lucabotez/OpenBook/Images/3D PCB.JPG

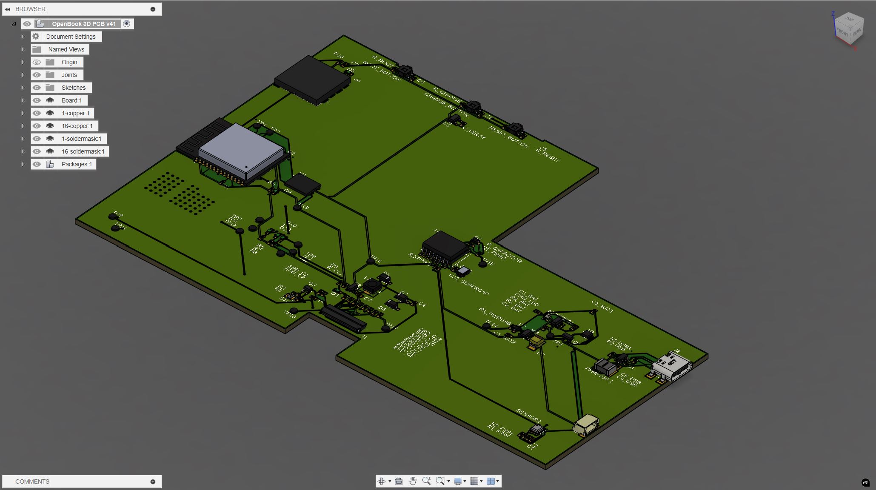
Images/3D PCB.JPG
