lucabotez/OpenBook/Images/Assembled OpenBook.JPG

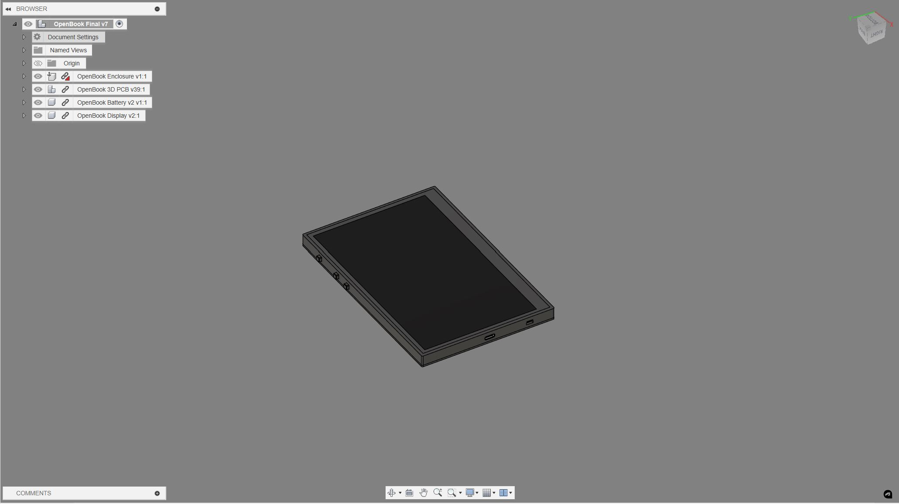
Images/Assembled OpenBook.JPG
